ClockWorks001/PIC32MX130_WaveClock_Mono/CheckProject.X/★★チェック用プロジェクト_02.JPG

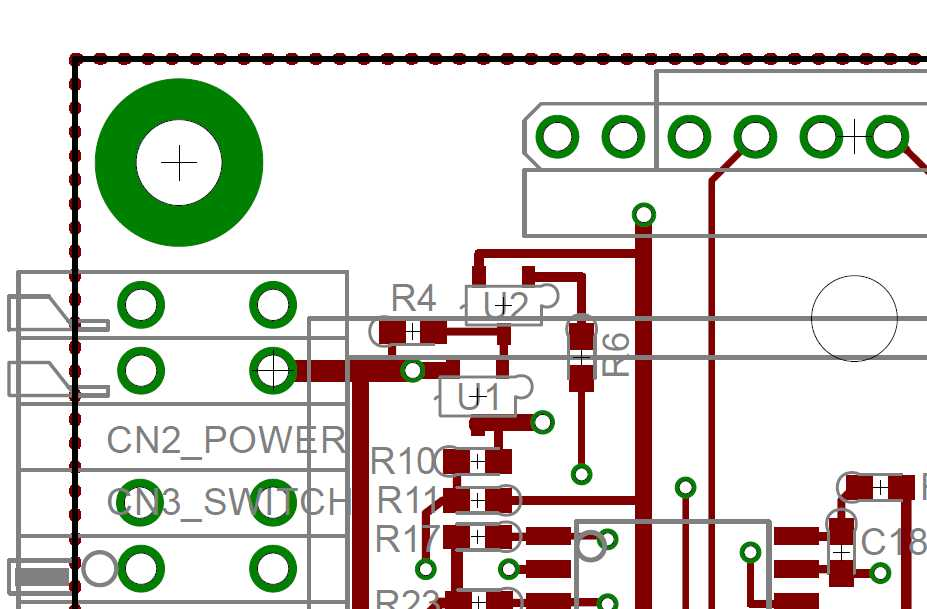
CheckProject.X/★★チェック用プロジェクト_02.JPG
