ClockWorks001/PIC32MX130_WaveClock_Mono/JWCAD/WS000728.JPG

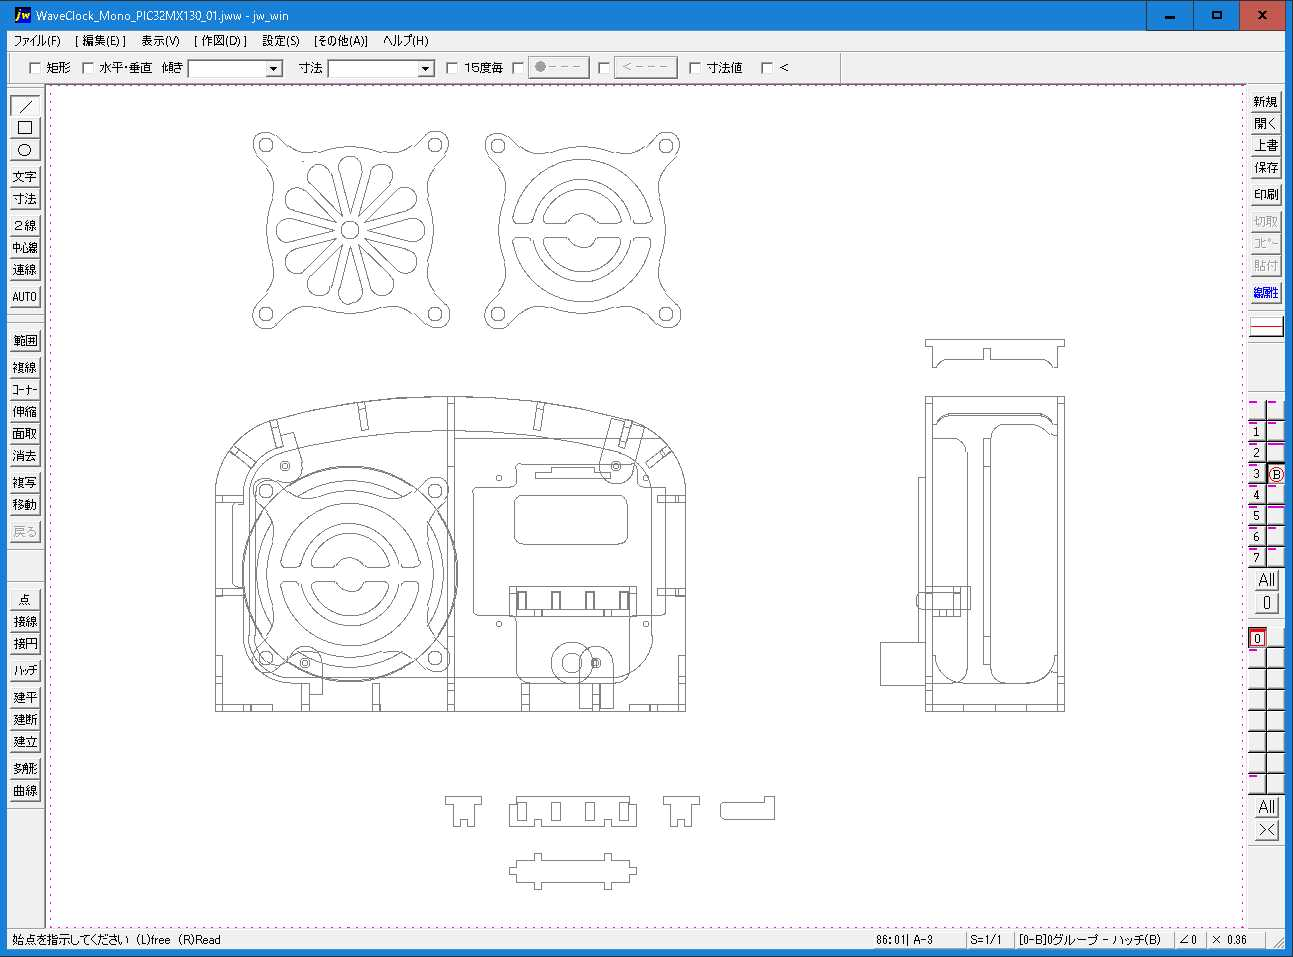
JWCAD/WS000728.JPG
