ClockWorks001/PIC32MX130_WaveClock_Mono/組み立て参考情報/IMG_1257.JPG

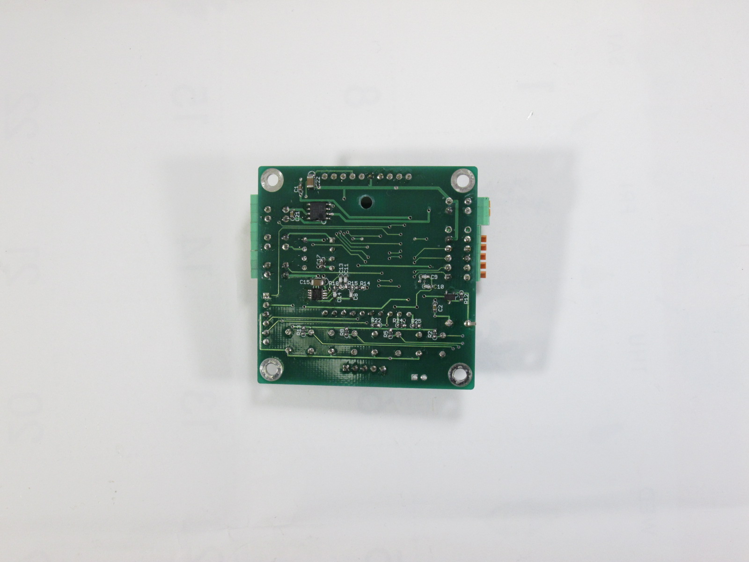
組み立て参考情報/IMG_1257.JPG
