ClockWorks001/PIC32MX130_WaveClock_Mono/組み立て参考情報/SDカードコネクタの取り付け位置②.JPG

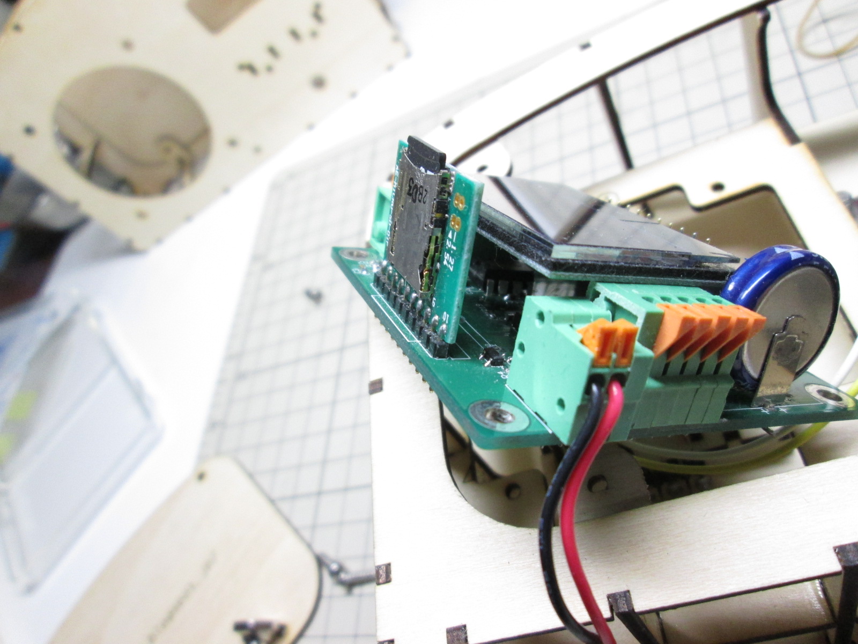
組み立て参考情報/SDカードコネクタの取り付け位置②.JPG
