ClockWorks001/PIC32MX130_WaveClock_Mono/組み立て参考情報【ケース】/IMG_1261.JPG

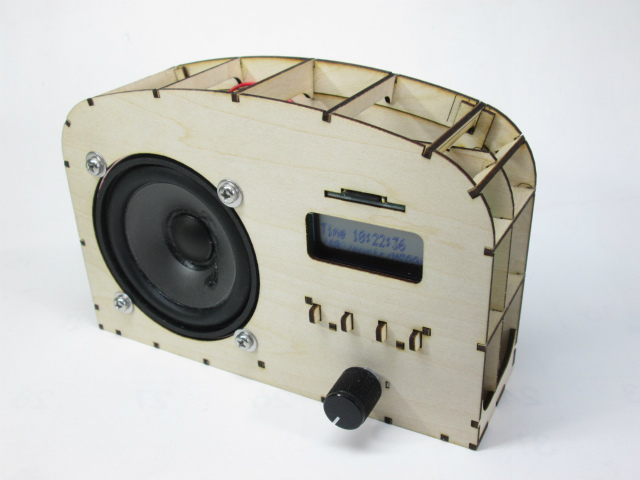
組み立て参考情報【ケース】/IMG_1261.JPG
