ClockWorks001/PIC32MX130_WaveClock_Mono/WaveClock006.X/user.h

/******************************************************************************/
/* User Level #define Macros                                                  */
/******************************************************************************/

/* TODO Application specific user parameters used in user.c may go here */

/******************************************************************************/
/* User Function Prototypes                                                    /
/******************************************************************************/

/* TODO User level functions prototypes (i.e. InitApp) go here */

void InitApp(void);         // I/O and Peripheral Initialization
void user_main(void);     // UART SAMPLE MAIN
